Kingdragoncat/Knox-Key/design-images/01_swd_header_pads.png

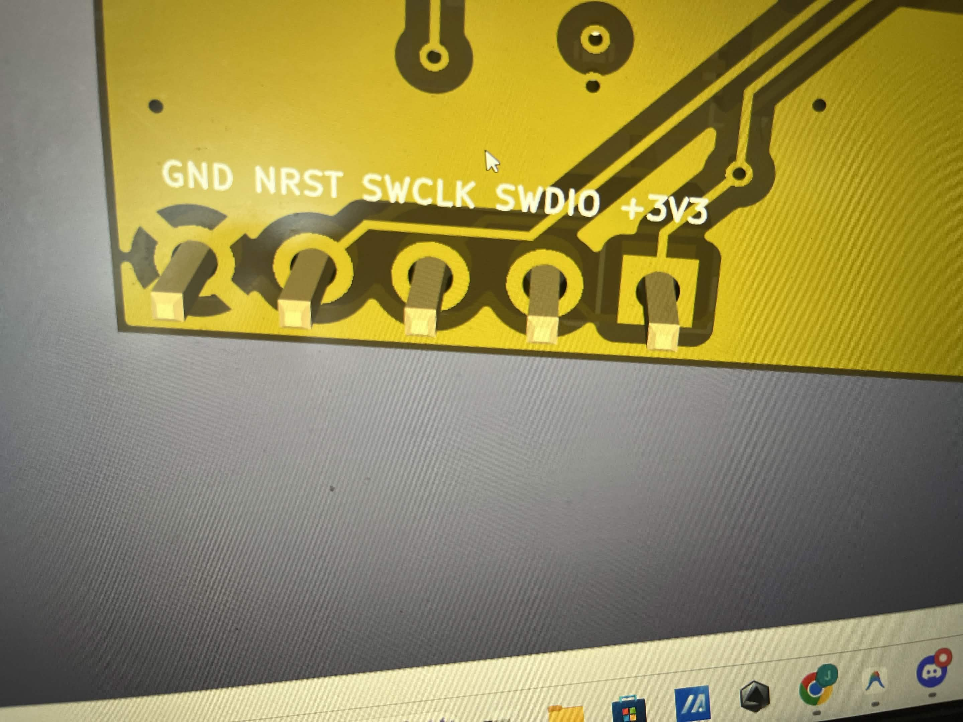
design-images/01_swd_header_pads.png
