Kingdragoncat/Knox-Key/design-images/12_header_pins_3d.png

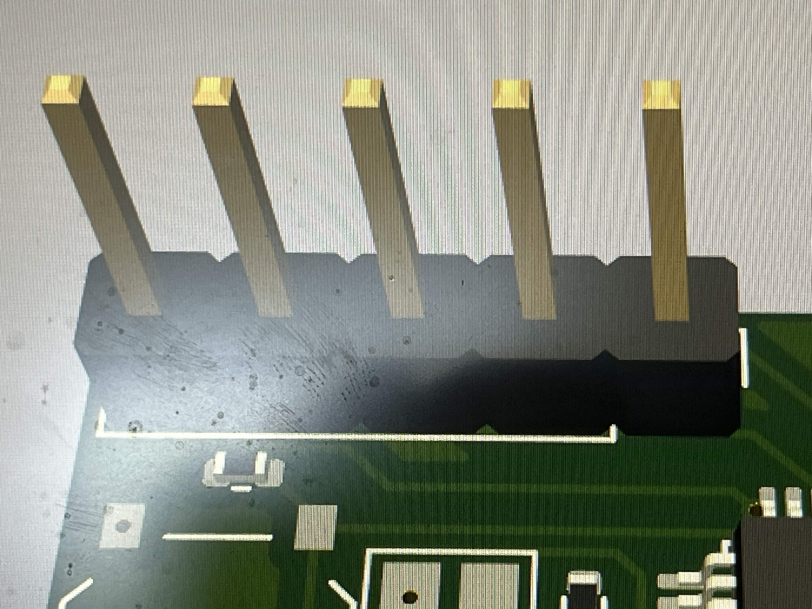
design-images/12_header_pins_3d.png
