Kingdragoncat/Knox-Key/firmware/knoxkey/core/ctaphid.c

#include "ctaphid.h"
#include "utils.h"
#include <string.h>
#include <stdbool.h>

/**
 * Allocates a channel ID for a new channel
 *
 * The current implementation allocates Channel IDs (CIDs)'in ascending order
 * starting with 1, 2, 3, ... (0xFFFFFFFF - 1).
 *
 * The value 0 is a reserved value and if returned y this function,
 * it indicates an error (all possible CIDs allocated).
 *
 * The value 0xFFFFFFFF is a reserved value (CTAPHID_BROADCAST_CID) and it is never returned by this function.
 *
 * @param state
 * @return a valid channel ID or 0 when there is no channel ID left
 *         (i.e., when we already allocated 2^32 - 2 channels are there are no numbers left)
 */
uint32_t ctaphid_allocate_channel(ctaphid_state_t *state) {
	if (state->highest_allocated_cid + 1 == CTAPHID_BROADCAST_CID) {
		return 0;
	}
	return ++state->highest_allocated_cid;
}

void ctaphid_create_init_packet(
	ctaphid_packet_t *packet,
	uint32_t cid,
	uint8_t cmd,
	size_t payload_length
) {
	assert((cmd & 0x80) == 0x80);
	assert(payload_length <= CTAPHID_MAX_PAYLOAD_LENGTH);
	assert(payload_length <= 0xFFFF);
	memset(packet, 0, sizeof(ctaphid_packet_t));
	packet->cid = cid;
	packet->pkt.init.cmd = cmd;
	packet->pkt.init.bcnt = lion_htons(payload_length);
}

void ctaphid_create_error_packet(ctaphid_packet_t *packet, uint32_t cid, uint8_t error_code) {
	ctaphid_create_init_packet(packet, cid, CTAPHID_ERROR, 1);
	packet->pkt.init.payload[0] = error_code;
}

void ctaphid_create_ctaphid_init_response_packet(
	ctaphid_packet_t *packet,
	const uint8_t *nonce,
	uint32_t transport_cid,
	uint32_t response_cid,
	uint8_t version_major,
	uint8_t version_minor,
	uint8_t version_build,
	uint8_t capabilities
) {
	ctaphid_create_init_packet(
		packet,
		transport_cid,
		CTAPHID_INIT,
		sizeof(ctaphid_init_response_payload_t)
	);
	ctaphid_init_response_payload_t *init_res = (ctaphid_init_response_payload_t *) packet->pkt.init.payload;
	memcpy(init_res->nonce, nonce, sizeof(init_res->nonce));
	init_res->cid = response_cid;
	init_res->protocol_version = CTAPHID_PROTOCOL_VERSION;
	init_res->version_major = version_major;
	init_res->version_minor = version_minor;
	init_res->version_build = version_build;
	init_res->capabilities = capabilities;
}

void ctaphid_message_to_packets(
	uint32_t cid,
	uint8_t cmd,
	size_t payload_length,
	const uint8_t *payload,
	ctap_packet_handler_t on_packet,
	void *on_packet_ctx
) {
	assert(payload_length <= CTAPHID_MAX_PAYLOAD_LENGTH);
	assert(payload_length <= 0xFFFF);
	assert(payload_length == 0 || payload != NULL);
	assert(on_packet != NULL);

	ctaphid_packet_t packet;

	// 11.2.4. Message and packet structure
	// https://fidoalliance.org/specs/fido-v2.1-ps-20210615/fido-client-to-authenticator-protocol-v2.1-ps-errata-20220621.html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

	// init packet
	// note that ctaphid_create_init_packet() fills the whole packet with zeros (including the payload)
	ctaphid_create_init_packet(
		&packet,
		cid,
		cmd,
		payload_length
	);
	// fast path
	if (payload_length == 0) {
		dump_hex((const uint8_t *) &packet, sizeof(packet));
		on_packet(&packet, on_packet_ctx);
		return;
	}
	const size_t init_packet_data_size = min(payload_length, CTAPHID_PACKET_INIT_PAYLOAD_SIZE);
	memcpy(&packet.pkt.init.payload, payload, init_packet_data_size);
	// no need to zero the rest of the payload (ctaphid_create_init_packet() already ensures that)
	dump_hex((const uint8_t *) &packet, sizeof(packet));
	on_packet(&packet, on_packet_ctx);

	// continuation packets (if necessary)
	size_t offset = init_packet_data_size;
	size_t remaining_data_size = payload_length - init_packet_data_size;
	uint8_t seq = 0;
	while (remaining_data_size > 0) {

		packet.cid = cid;
		packet.pkt.cont.seq = seq;
		size_t payload_size = min(remaining_data_size, CTAPHID_PACKET_CONT_PAYLOAD_SIZE);
		memcpy(packet.pkt.cont.payload, &payload[offset], payload_size);
		if (payload_size < CTAPHID_PACKET_CONT_PAYLOAD_SIZE) {
			memset(&packet.pkt.cont.payload[payload_size], 0, CTAPHID_PACKET_CONT_PAYLOAD_SIZE - payload_size);
		}
		dump_hex((const uint8_t *) &packet, sizeof(packet));
		on_packet(&packet, on_packet_ctx);

		assert(remaining_data_size >= payload_size);
		remaining_data_size -= payload_size;
		offset += payload_size;
		++seq;

	}

}

static inline bool is_idle(const ctaphid_channel_buffer_t *buffer) {
	return buffer->cid == 0;
}

static inline bool is_complete_message(const ctaphid_channel_buffer_t *buffer) {
	return buffer->offset == buffer->payload_length;
}

static inline bool is_complete_message_cmd(const ctaphid_channel_buffer_t *buffer, const uint8_t cmd) {
	return buffer->cmd == cmd && is_complete_message(buffer);
}

static inline bool is_incomplete_message(const ctaphid_channel_buffer_t *buffer) {
	return buffer->offset < buffer->payload_length;
}

bool ctaphid_is_idle(const ctaphid_state_t *state) {
	const ctaphid_channel_buffer_t *buffer = &state->buffer;
	assert(buffer->cid != CTAPHID_BROADCAST_CID);
	return is_idle(buffer);
}

bool ctaphid_has_complete_message_ready(const ctaphid_state_t *state) {
	const ctaphid_channel_buffer_t *buffer = &state->buffer;
	assert(buffer->cid != CTAPHID_BROADCAST_CID);
	if (is_idle(buffer)) {
		return false;
	}
	assert(buffer->cmd != 0);
	return is_complete_message(buffer);
}

/**
 * Returns true if a transaction timeout occurred and the current incomplete message should be discarded
 *
 * This function can be used to implement 11.2.5.2. Transaction timeout:
 *   A transaction has to be completed within a specified period of time
 *   to prevent a stalling application to cause the device to be completely
 *   locked out for access by other applications.
 *
 * This check is not a part of the ctaphid_process_packet() so that the caller
 * can send an error (e.g., CTAP1_ERR_TIMEOUT) on the channel with the timeout
 * before the buffer is reset.
 *
 * @param state the current CTAPHID state
 * @retval true iff there is an incomplete message in the buffer and CTAPHID_TRANSACTION_TIMEOUT time
 *         has elapsed since the initialization packet (of the current incomplete message) was processed.
 *         The caller can send an error (e.g., CTAP1_ERR_TIMEOUT) on the channel with the timeout
 *         and then it should reset the buffer (ctaphid_reset_to_idle()) so that receiving (assembling)
 *         of a new message on any valid (allocated) channel can start in ctaphid_process_packet().
 * @retval false otherwise (i.e., idle, or an incomplete message within the time limit, or a complete message
 */
bool ctaphid_has_incomplete_message_timeout(const ctaphid_state_t *state, uint32_t current_time) {

	const ctaphid_channel_buffer_t *const buffer = &state->buffer;

	if (is_incomplete_message(buffer)) {

		assert(buffer->cid != CTAPHID_BROADCAST_CID);
		assert(buffer->cmd != 0);

		const uint32_t elapsed_since_init_packet = current_time - buffer->start_time;
		if (elapsed_since_init_packet > CTAPHID_TRANSACTION_TIMEOUT) {
			return true;
		}

	}

	return false;

}

static void reset_buffer(ctaphid_channel_buffer_t *buffer) {
	buffer->start_time = 0;
	buffer->cid = 0;
	buffer->cmd = 0;
	buffer->cancel = false;
	buffer->payload_length = 0;
	buffer->next_seq = 0;
	buffer->offset = 0;
}

static ctaphid_process_packet_result_t copy_payload_to_buffer(
	ctaphid_channel_buffer_t *buffer,
	const uint8_t *packet_payload,
	size_t packet_payload_size
) {
	assert(buffer->payload_length >= buffer->offset);
	size_t remaining_size = buffer->payload_length - buffer->offset;

	size_t copy_size = min(packet_payload_size, remaining_size);

	assert(buffer->offset + copy_size <= sizeof(buffer->payload));
	memcpy(&buffer->payload[buffer->offset], packet_payload, copy_size);
	buffer->offset += copy_size;

	if (is_complete_message(buffer)) {
		debug_log(green("  request message ready") nl);
		return CTAPHID_RESULT_MESSAGE;
	}

	debug_log("  buffered" nl);
	assert(is_incomplete_message(buffer));
	return CTAPHID_RESULT_BUFFERING;
}

static inline bool is_initialization_packet(const ctaphid_packet_t *packet) {
	return packet->pkt.init.cmd & CTAPHID_PACKET_TYPE_INIT;
}

static inline bool is_continuation_packet(const ctaphid_packet_t *packet) {
	return !is_initialization_packet(packet);
}

void ctaphid_init(ctaphid_state_t *state) {
	debug_log("ctaphid_init" nl);
	state->highest_allocated_cid = 0;
	reset_buffer(&state->buffer);
}

void ctaphid_reset_to_idle(ctaphid_state_t *state) {
	debug_log("ctaphid_reset_to_idle" nl);
	reset_buffer(&state->buffer);
}

/**
 * Updates the CTAPHID state by processing a CTAPHID packet (a HID report)
 */
ctaphid_process_packet_result_t ctaphid_process_packet(
	ctaphid_state_t *state,
	const ctaphid_packet_t *packet,
	uint32_t current_time,
	uint8_t *error_code
) {
	ctaphid_channel_buffer_t *buffer = &state->buffer;

	if (is_initialization_packet(packet)) {
		debug_log(
			"ctaphid_process_packet"
			" cid=0x%08" PRIx32 " "
			cyan("initialization")
			" cmd=0x%02" wPRIx8
			" payload_length=%" PRIu16 nl,
			packet->cid,
			packet->pkt.init.cmd,
			lion_ntohs(packet->pkt.init.bcnt)
		);
	} else {
		debug_log(
			"ctaphid_process_packet"
			" cid=0x%08" PRIx32 " "
			magenta("continuation")
			" seq=0x%02" wPRIx8 nl,
			packet->cid,
			packet->pkt.cont.seq
		);
	}

	// validate channel id
	if (packet->cid == 0 || packet->cid > state->highest_allocated_cid) {
		if (packet->cid == CTAPHID_BROADCAST_CID && packet->pkt.init.cmd == CTAPHID_INIT) {
			// The special CTAPHID_BROADCAST_CID value is only allowed with the CTAPHID_INIT command.
			// Note that packet->pkt.init.cmd == CTAPHID_INIT implies is_initialization_packet(packet) == true
			// (since we defined CTAPHID_INIT as (CTAPHID_PACKET_TYPE_INIT | 0x06)).
		} else {
			debug_log(red("  error: invalid channel") nl);
			*error_code = CTAP1_ERR_INVALID_CHANNEL;
			return CTAPHID_RESULT_ERROR;
		}
	}

		if (packet->pkt.init.cmd == CTAPHID_CANCEL) {
			if (lion_ntohs(packet->pkt.init.bcnt) != 0) {
				*error_code = CTAP1_ERR_INVALID_LENGTH;
				return CTAPHID_RESULT_ERROR;
			}
			if (packet->cid == buffer->cid && is_complete_message_cmd(buffer, CTAPHID_CBOR)) {
				buffer->cancel = true;
				return CTAPHID_RESULT_CANCEL;
			}
			debug_log(red("  ignored CTAPHID_CANCEL") nl);
			return CTAPHID_RESULT_IGNORED;
		}

		if (packet->pkt.init.cmd == CTAPHID_INIT) {
			if (lion_ntohs(packet->pkt.init.bcnt) != 8) {
				*error_code = CTAP1_ERR_INVALID_LENGTH;
				return CTAPHID_RESULT_ERROR;
			}
			if (packet->cid == CTAPHID_BROADCAST_CID) {
				return CTAPHID_RESULT_ALLOCATE_CHANNEL;
			}
			assert(packet->cid != 0 && packet->cid <= state->highest_allocated_cid);
			if (packet->cid == buffer->cid && is_incomplete_message(buffer)) {
				reset_buffer(buffer);
			}
			return CTAPHID_RESULT_DISCARD_INCOMPLETE_MESSAGE;
		}

		// 1.2.5.1. Transaction atomicity, idle and busy states
		//   The application channel that manages to get through the first **initialization packet**
		//   when the device is in **idle state** will keep the device locked for other channels
		//   until the last packet of the response message has been received or the transaction is aborted.

		// validate the payload length
		if (lion_ntohs(packet->pkt.init.bcnt) > sizeof(buffer->payload)) {
			debug_log(red("  error: payload length exceeded sizeof(buffer->payload)") nl);
			*error_code = CTAP1_ERR_INVALID_LENGTH;
			return CTAPHID_RESULT_ERROR;
		}

		if (!is_idle(buffer)) {
			debug_log(red("  error: init packet while channel busy") nl);
			*error_code = CTAP1_ERR_CHANNEL_BUSY;
			return CTAPHID_RESULT_ERROR;
		}

		assert(packet->cid != 0 && packet->cid <= state->highest_allocated_cid);
		buffer->start_time = current_time;
		buffer->cid = packet->cid;
		assert(packet->pkt.init.cmd != CTAPHID_CANCEL && packet->pkt.init.cmd != CTAPHID_INIT);
		buffer->cmd = packet->pkt.init.cmd;
		buffer->cancel = false;
		buffer->payload_length = lion_ntohs(packet->pkt.init.bcnt);
		buffer->next_seq = 0;
		buffer->offset = 0;
		return copy_payload_to_buffer(buffer, packet->pkt.init.payload, CTAPHID_PACKET_INIT_PAYLOAD_SIZE);

	}

	assert(is_continuation_packet(packet));

	if (buffer->cid != packet->cid) {
		// 11.2.5.4. Packet sequencing
		// Spurious continuation packets appearing without a prior initialization packet will be ignored.
		debug_log(red("  spurious continuation packet ignored") nl);
		return CTAPHID_RESULT_IGNORED;
	}

	assert(buffer->cid == packet->cid);
	assert(buffer->cmd != 0);
	assert(buffer->payload_length != 0);
	if (buffer->next_seq != packet->pkt.cont.seq) {
		*error_code = CTAP1_ERR_INVALID_SEQ;
		debug_log(
			red("  invalid seq: expected=%" wPRIu8 " got=%" wPRIu8) nl,
			buffer->next_seq, packet->pkt.cont.seq
		);
		return CTAPHID_RESULT_ERROR;
	}
	buffer->next_seq++;
	return copy_payload_to_buffer(buffer, packet->pkt.cont.payload, CTAPHID_PACKET_CONT_PAYLOAD_SIZE);

}

#if knoxkey_DEBUG_LEVEL > 0
const char *const debug_str_ctaphid_process_packet_result[] = {
	[CTAPHID_RESULT_ERROR] = "CTAPHID_RESULT_ERROR",
	[CTAPHID_RESULT_IGNORED] = "CTAPHID_RESULT_IGNORED",
	[CTAPHID_RESULT_CANCEL] = "CTAPHID_RESULT_CANCEL",
	[CTAPHID_RESULT_ALLOCATE_CHANNEL] = "CTAPHID_RESULT_ALLOCATE_CHANNEL",
	[CTAPHID_RESULT_DISCARD_INCOMPLETE_MESSAGE] = "CTAPHID_RESULT_DISCARD_INCOMPLETE_MESSAGE",
	[CTAPHID_RESULT_BUFFERING] = "CTAPHID_RESULT_BUFFERING",
	[CTAPHID_RESULT_MESSAGE] = "CTAPHID_RESULT_MESSAGE",
};
#endif
