Kingdragoncat/Knox-Key/firmware/knoxkey/core/ctaphid.h

#ifndef knoxkey_CTAPHID_H
#define knoxkey_CTAPHID_H

#include <stdint.h>
#include <stddef.h>
#include <stdbool.h>
#include <assert.h>
#include "ctap_errors.h"
#include "compiler.h"
#include "debug.h"

// 11.2.2. Protocol structure and data framing
// https://fidoalliance.org/specs/fido-v2.1-ps-20210615/fido-client-to-authenticator-protocol-v2.1-ps-errata-20220621.html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
//   Transaction
//      1. Request message (one or more packets) (sent from a host to a device)
//      2. Response message (one or more packets) (sent from a device back to the host)
//      * Once a request has been initiated, the transaction has to be entirely completed
//      or aborted before a second transaction can take place.
//      * A response is never sent without a previous request.
//   Message
//     Request and response messages are in turn divided into individual fragments,
//     known as packets. The packet is the smallest form of protocol data unit,
//     which in the case of CTAPHID are mapped into HID reports.
//   Packet == HID report

// This must be equal to the HID report size.
#ifndef CTAPHID_PACKET_SIZE
#define CTAPHID_PACKET_SIZE 64
#endif

#ifndef CTAPHID_TRANSACTION_TIMEOUT
#define CTAPHID_TRANSACTION_TIMEOUT 2000 // ms
#endif

// 11.2.4. Message and packet structure
// https://fidoalliance.org/specs/fido-v2.1-ps-20210615/fido-client-to-authenticator-protocol-v2.1-ps-errata-20220621.html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
#define CTAPHID_PACKET_TYPE_INIT 0x80
#define CTAPHID_PACKET_TYPE_CONT 0x00

// 11.2.9. CTAPHID commands
// 11.2.9.1. Mandatory commands
typedef enum LION_ATTR_PACKED ctaphid_command {
	// https://fidoalliance.org/specs/fido-v2.1-ps-20210615/fido-client-to-authenticator-protocol-v2.1-ps-errata-20220621.html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
	CTAPHID_PING = (CTAPHID_PACKET_TYPE_INIT | 0x01),
	CTAPHID_MSG = (CTAPHID_PACKET_TYPE_INIT | 0x03),
	CTAPHID_INIT = (CTAPHID_PACKET_TYPE_INIT | 0x06),
	CTAPHID_CBOR = (CTAPHID_PACKET_TYPE_INIT | 0x10),
	CTAPHID_CANCEL = (CTAPHID_PACKET_TYPE_INIT | 0x11),
	CTAPHID_ERROR = (CTAPHID_PACKET_TYPE_INIT | 0x3F),
	CTAPHID_KEEPALIVE = (CTAPHID_PACKET_TYPE_INIT | 0x3B),
	// 11.2.9.2. Optional commands
	// https://fidoalliance.org/specs/fido-v2.1-ps-20210615/fido-client-to-authenticator-protocol-v2.1-ps-errata-20220621.html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
	CTAPHID_LOCK = (CTAPHID_PACKET_TYPE_INIT | 0x04),
	CTAPHID_WINK = (CTAPHID_PACKET_TYPE_INIT | 0x08),
	// 11.2.9.3. Vendor specific commands
	// https://fidoalliance.org/specs/fido-v2.1-ps-20210615/fido-client-to-authenticator-protocol-v2.1-ps-errata-20220621.html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
	CTAPHID_VENDOR_FIRST = (CTAPHID_PACKET_TYPE_INIT | 0x40),
	CTAPHID_VENDOR_LAST = (CTAPHID_PACKET_TYPE_INIT | 0x7F),
} ctaphid_command_t;
static_assert(sizeof(ctaphid_command_t) == sizeof(uint8_t), "invalid sizeof(ctaphid_command_t)");
#define ctaphid_get_cmd_number_per_spec(cmd) ((cmd) & ~CTAPHID_PACKET_TYPE_INIT)

// defined in 11.2.9.1.3. CTAPHID_INIT (0x06):
//   Response at success:
//     DATA+12: CTAPHID protocol version identifier
//     >> The protocol version identifies the protocol version implemented by the device.
//        This version of the CTAPHID protocol is 2.
// https://fidoalliance.org/specs/fido-v2.1-ps-20210615/fido-client-to-authenticator-protocol-v2.1-ps-errata-20220621.html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
#define CTAPHID_PROTOCOL_VERSION    2

#define CTAPHID_PACKET_INIT_PAYLOAD_SIZE  (CTAPHID_PACKET_SIZE - 7)
#define CTAPHID_PACKET_CONT_PAYLOAD_SIZE  (CTAPHID_PACKET_SIZE - 5)

// 1.2.3. Concurrency and channels
// >> Channel ID 0 is reserved and 0xffffffff is reserved for broadcast commands,
//    i.e. at the time of channel allocation.
// https://fidoalliance.org/specs/fido-v2.1-ps-20210615/fido-client-to-authenticator-protocol-v2.1-ps-errata-20220621.html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
#define CTAPHID_BROADCAST_CID 0xffffffff

// 11.2.4. Message and packet structure
// https://fidoalliance.org/specs/fido-v2.1-ps-20210615/fido-client-to-authenticator-protocol-v2.1-ps-errata-20220621.html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
// >> With a packet size of 64 bytes (max for full-speed devices),
//    this means that the maximum message payload length is (64 - 7) + (128 * (64 - 5)) = 7609 bytes.
// one initialization packet + 128 continuation packets (packet sequence number is the 7-bit SEQ = 0..127 -> 128)
#ifndef CTAPHID_MAX_PAYLOAD_LENGTH
#define CTAPHID_MAX_PAYLOAD_LENGTH (CTAPHID_PACKET_INIT_PAYLOAD_SIZE + (128 * CTAPHID_PACKET_CONT_PAYLOAD_SIZE))
#define CTAPHID_MAX_PAYLOAD_LENGTH_IS_DEFAULT 1
#endif
// 1 initialization packet + 128 continuation packets (packet sequence number is the 7-bit SEQ = 0..127 -> 128)
#define CTAPHID_MESSAGE_MAX_NUM_PACKETS (1 + 128)
// a static assert with one test case to make sure our CTAPHID size-related macros work correctly
#ifdef CTAPHID_MAX_PAYLOAD_LENGTH_IS_DEFAULT
static_assert(
	CTAPHID_PACKET_SIZE != 64 || CTAPHID_MAX_PAYLOAD_LENGTH == 7609,
	"The following implication must hold: (CTAPHID_PACKET_SIZE == 64) => (CTAPHID_MAX_PAYLOAD_LENGTH == 7609)"
);
#endif

// defined in 11.2.9.1.3. CTAPHID_INIT (0x06)
// https://fidoalliance.org/specs/fido-v2.1-ps-20210615/fido-client-to-authenticator-protocol-v2.1-ps-errata-20220621.html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
#define CTAPHID_CAPABILITY_WINK 0x01
#define CTAPHID_CAPABILITY_LOCK 0x02
#define CTAPHID_CAPABILITY_CBOR 0x04
#define CTAPHID_CAPABILITY_NMSG 0x08

// 11.2.4. Message and packet structure
// https://fidoalliance.org/specs/fido-v2.1-ps-20210615/fido-client-to-authenticator-protocol-v2.1-ps-errata-20220621.html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
typedef struct LION_ATTR_PACKED ctaphid_packet {
	uint32_t cid; // Channel identifier
	union {
		struct LION_ATTR_PACKED ctaphid_packet_init {
			uint8_t cmd; // Command identifier (bit 7 always set)
			// uint8_t bcnth; // High part of payload length
			// uint8_t bcntl; // Low part of payload length
			uint16_t bcnt; // Payload length (stored in big-endian)
			uint8_t payload[CTAPHID_PACKET_INIT_PAYLOAD_SIZE];
		} init;
		struct LION_ATTR_PACKED ctaphid_packet_cont {
			uint8_t seq; // Packet sequence 0x00..0x7f (bit 7 always cleared)
			uint8_t payload[CTAPHID_PACKET_CONT_PAYLOAD_SIZE];
		} cont;
	} pkt;
} ctaphid_packet_t;
static_assert(
	sizeof(ctaphid_packet_t) == CTAPHID_PACKET_SIZE,
	"unexpected sizeof(ctaphid_packet_t)"
);
// for some reason sizeof(struct ctaphid_packet_init) and sizeof(struct ctaphid_packet_cont)
// result in compile errors when compiling in C++ (when this header is included from C++ source)
#ifndef __cplusplus
static_assert(
	sizeof(struct ctaphid_packet_init) == CTAPHID_PACKET_SIZE - sizeof(uint32_t),
	"unexpected sizeof(struct ctaphid_packet_init)"
);
static_assert(
	sizeof(struct ctaphid_packet_cont) == CTAPHID_PACKET_SIZE - sizeof(uint32_t),
	"unexpected sizeof(struct ctaphid_packet_cont)"
);
#endif

// 11.2.9.1.3. CTAPHID_INIT (0x06)
// https://fidoalliance.org/specs/fido-v2.1-ps-20210615/fido-client-to-authenticator-protocol-v2.1-ps-errata-20220621.html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
// Response at success
typedef struct LION_ATTR_PACKED ctaphid_init_response_payload {
	uint8_t nonce[8];
	uint32_t cid;
	uint8_t protocol_version;
	uint8_t version_major;
	uint8_t version_minor;
	uint8_t version_build;
	uint8_t capabilities;
} ctaphid_init_response_payload_t;

static_assert(
	sizeof(ctaphid_init_response_payload_t) == 17,
	"unexpected sizeof(ctaphid_init_response_payload_t)"
);
static_assert(
	sizeof(ctaphid_init_response_payload_t) <= CTAPHID_PACKET_INIT_PAYLOAD_SIZE,
	"sizeof(ctaphid_init_response_payload_t) must be less than or equal to CTAPHID_PACKET_INIT_PAYLOAD_SIZE"
);


// This buffer is used to assemble the incoming (request) message on one specific channel.
// Message consists of one initialization packet and up to 128 continuation packets.
// see https://fidoalliance.org/specs/fido-v2.1-ps-20210615/fido-client-to-authenticator-protocol-v2.1-ps-errata-20220621.html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
typedef struct ctaphid_channel_buffer {
	uint32_t start_time;
	uint32_t cid;
	uint8_t cmd;
	bool cancel;
	size_t payload_length;
	uint8_t next_seq;
	size_t offset;
	uint8_t payload[CTAPHID_MAX_PAYLOAD_LENGTH];
} ctaphid_channel_buffer_t;

typedef struct ctaphid_state {

	// Channel IDs (CIDs) are allocated in ascending order starting with 1, 2, 3, ... (0xFFFFFFFF - 1).
	// CID 0 is reserved.
	// CID 0xFFFFFFFF is reserved for broadcast commands.
	// see https://fidoalliance.org/specs/fido-v2.1-ps-20210615/fido-client-to-authenticator-protocol-v2.1-ps-errata-20220621.html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
	uint32_t highest_allocated_cid;

	ctaphid_channel_buffer_t buffer;

} ctaphid_state_t;

typedef enum ctaphid_process_packet_result {
	CTAPHID_RESULT_ERROR,
	CTAPHID_RESULT_IGNORED,
	CTAPHID_RESULT_CANCEL,
	CTAPHID_RESULT_ALLOCATE_CHANNEL,
	CTAPHID_RESULT_DISCARD_INCOMPLETE_MESSAGE,
	CTAPHID_RESULT_BUFFERING,
	CTAPHID_RESULT_MESSAGE,
} ctaphid_process_packet_result_t;
#if knoxkey_DEBUG_LEVEL > 0
extern const char *const debug_str_ctaphid_process_packet_result[];
#endif

void ctaphid_init(ctaphid_state_t *state);

void ctaphid_reset_to_idle(ctaphid_state_t *state);

uint32_t ctaphid_allocate_channel(ctaphid_state_t *state);

ctaphid_process_packet_result_t ctaphid_process_packet(
	ctaphid_state_t *state,
	const ctaphid_packet_t *packet,
	uint32_t current_time,
	uint8_t *error_code
);

bool ctaphid_is_idle(const ctaphid_state_t *state);

bool ctaphid_has_complete_message_ready(const ctaphid_state_t *state);

bool ctaphid_has_incomplete_message_timeout(const ctaphid_state_t *state, uint32_t current_time);

void ctaphid_create_init_packet(
	ctaphid_packet_t *packet,
	uint32_t cid,
	uint8_t cmd,
	size_t payload_length
);

void ctaphid_create_error_packet(ctaphid_packet_t *packet, uint32_t cid, uint8_t error_code);

void ctaphid_create_ctaphid_init_response_packet(
	ctaphid_packet_t *packet,
	const uint8_t *nonce,
	uint32_t transport_cid,
	uint32_t response_cid,
	uint8_t version_major,
	uint8_t version_minor,
	uint8_t version_build,
	uint8_t capabilities
);

typedef void (*ctap_packet_handler_t)(const ctaphid_packet_t *packet, void *ctx);

void ctaphid_message_to_packets(
	uint32_t cid,
	uint8_t cmd,
	size_t payload_length,
	const uint8_t *payload,
	ctap_packet_handler_t on_packet,
	void *on_packet_ctx
);

#endif // knoxkey_CTAPHID_H
