Kingdragoncat/Knox-Key/firmware/knoxkey/core/utils.c

#include "utils.h"

#if knoxkey_DEBUG_LEVEL > 2

void dump_hex(const uint8_t *buf, size_t size) {
	debug_log("hex(%" PRIsz "): ", size);
	while (size--) {
		debug_log("%02" wPRIx8, *buf++);
	}
	debug_log(nl);
}

#endif
